LieBtrau/Click_BLE2_RN4020/Hardware/BRD161224/simulation/levelTranslator_powerSwitch.asc

R1: res; 100
R2: res; 100K
R3: res; 100K
U1: DMP2035U
U2: DMP2035U
U3: DMP2035U
U4: FDV301N
V1: voltage; 3.3
V2: voltage; PWL(0 0 0.5m 0 0.501m 3.3 1.5m 3.3 1.501m 0)
V3: voltage; PWL(0 0 1m 0 1.01m 3.3)
Named nets: 0, vcc, vgpio, reset
.tran 0 5m 0 uic
